LawrenceBrode/playstation.uno/IMG_0262.PNG

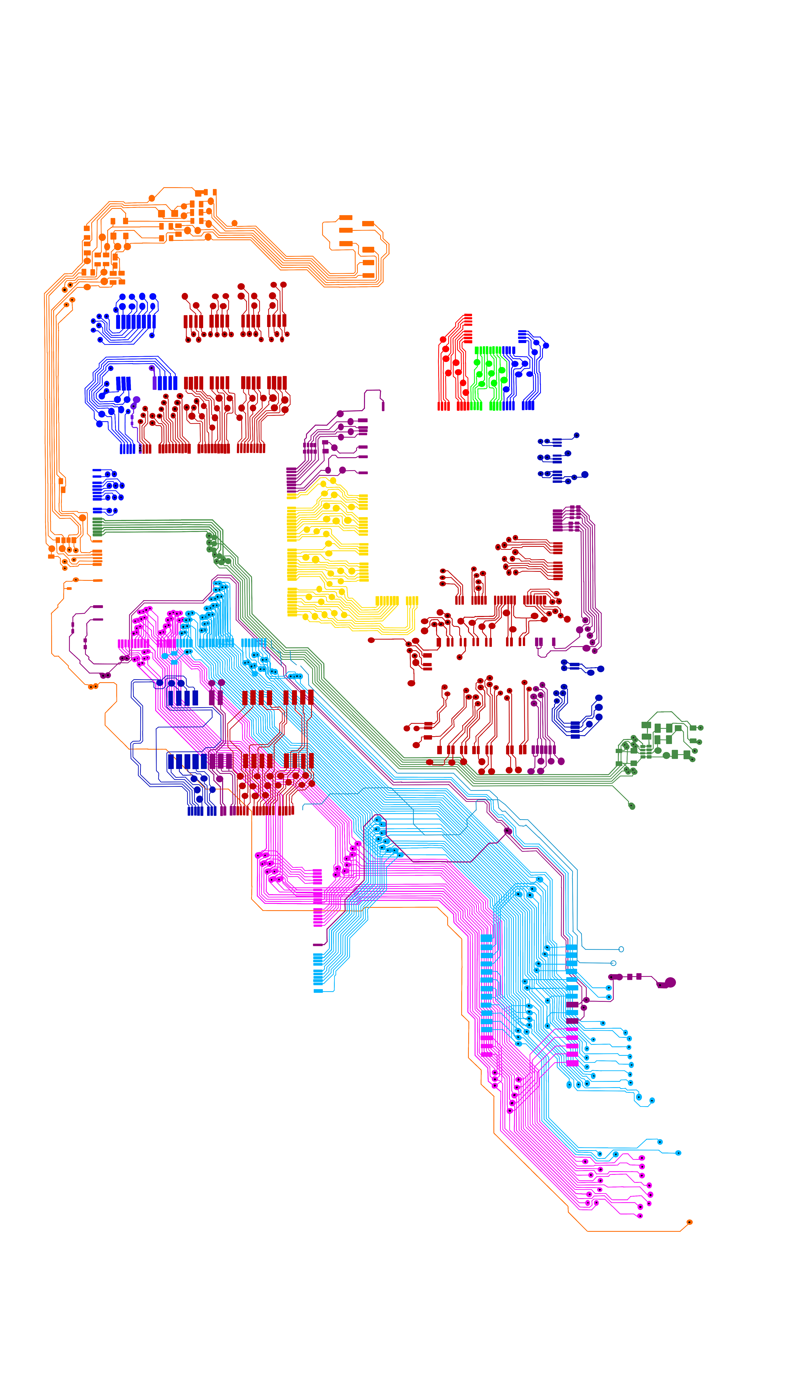
IMG_0262.PNG
